vvhg1/clp-keycaps/step/CLP_Base_Tilt7_1_5u.step

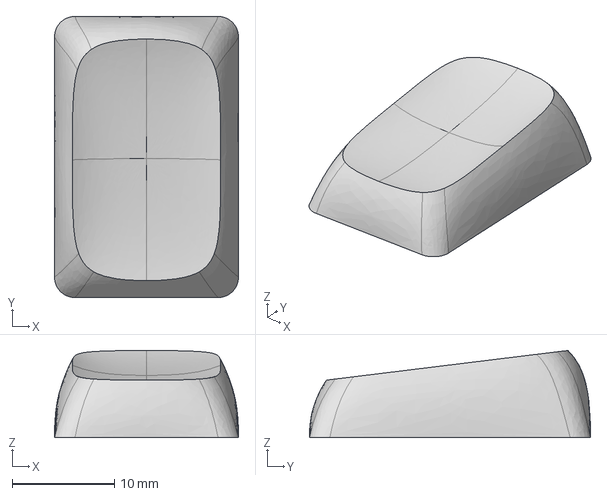
[picture p20: CAD file, 2026-10-05]
step/CLP_Base_Tilt7_1_5u.step
18.0 x 27.5 x 8.52 mm
