vvhg1/clp-keycaps/stl/CLP_Tilt7 v8.stl

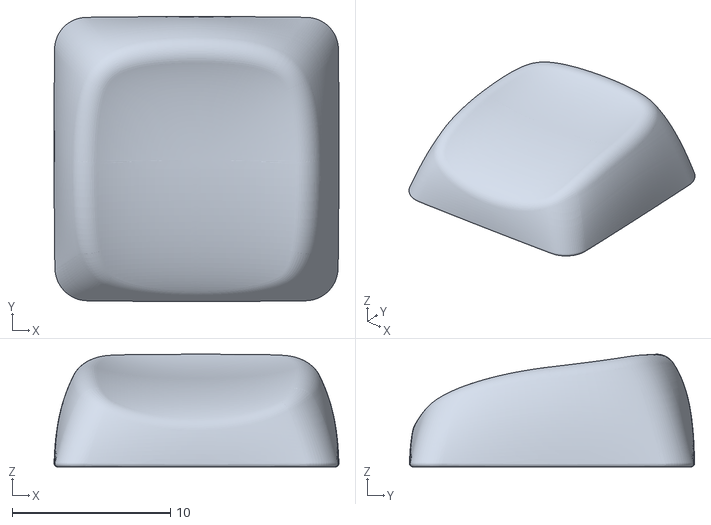
[picture p21: CAD file, 2023-11-12]
stl/CLP_Tilt7 v8.stl
18.0 x 18.0 x 7.11
