vvhg1/clp-keycaps/step/CLP_Base_Tilt14_R4.step

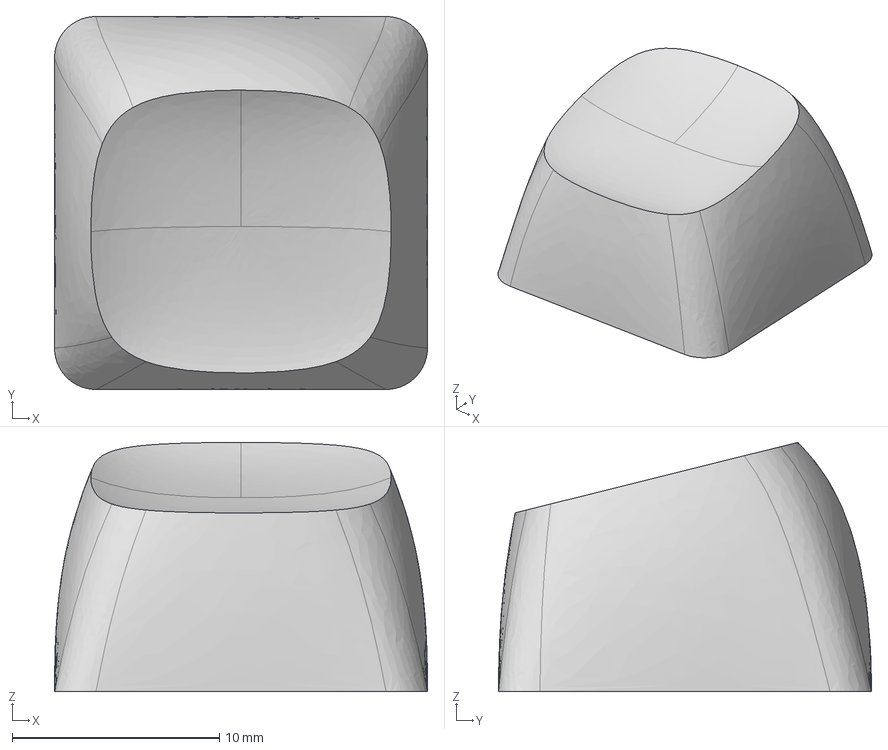
[picture p22: CAD file, 2026-10-05]
step/CLP_Base_Tilt14_R4.step
18.0 x 18.0 x 12.0 mm
