vvhg1/clp-keycaps/step/CLP_Base_Tilt14_Doubleslant.step

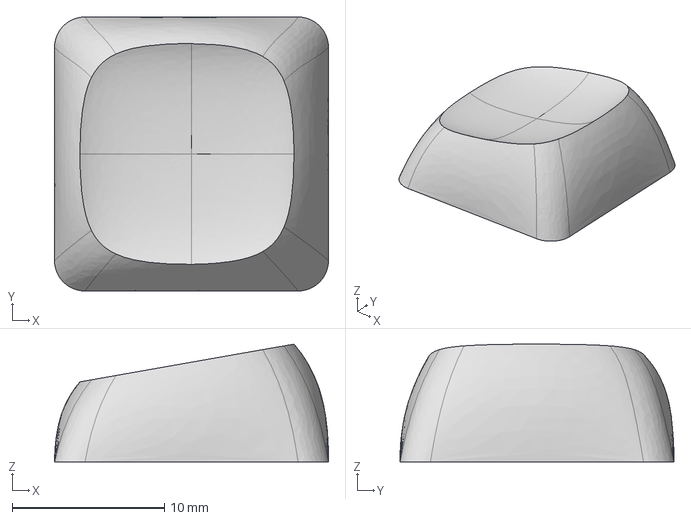
[picture p23: CAD file, 2026-10-05]
step/CLP_Base_Tilt14_Doubleslant.step
18.0 x 18.0 x 7.74 mm
