vvhg1/clp-keycaps/stl/CLP_Tilt7_1_5u v13.stl

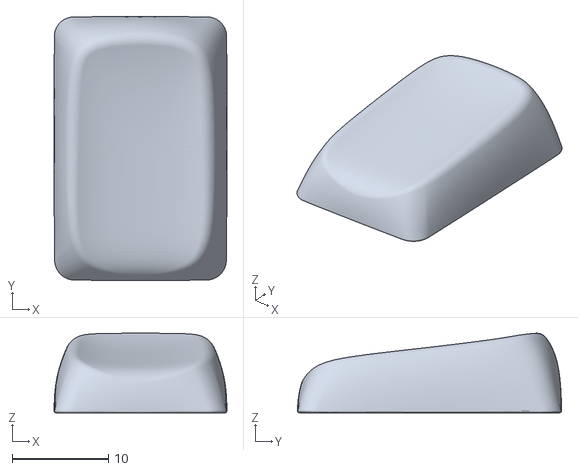
[picture p24: CAD file, 2023-11-12]
stl/CLP_Tilt7_1_5u v13.stl
18.0 x 27.5 x 8.30
