vvhg1/clp-keycaps/stl/CLP_Dished_Tilt14 v3.stl

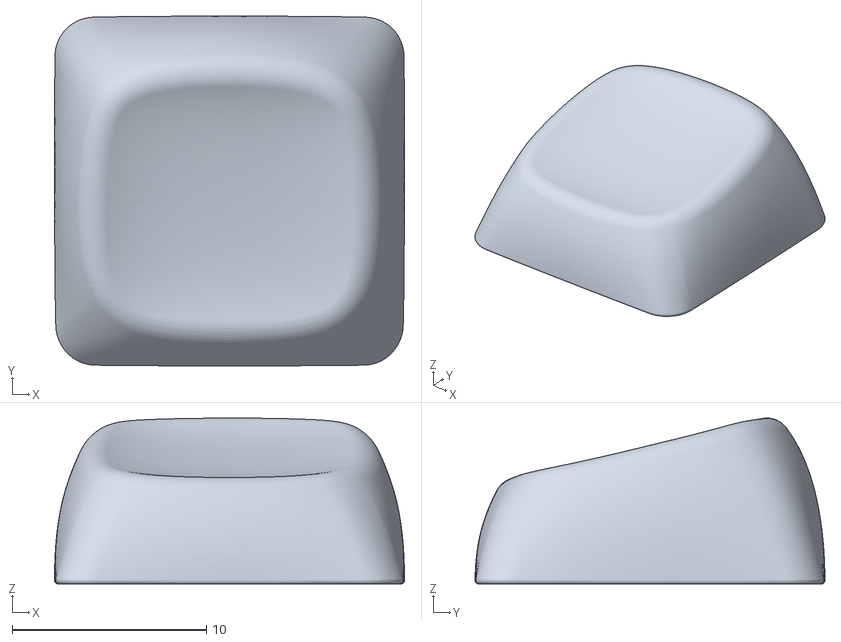
[picture p25: CAD file, 2023-11-12]
stl/CLP_Dished_Tilt14 v3.stl
18.0 x 18.0 x 8.53
