vvhg1/clp-keycaps/step/CLP_Base_Tilt7_R4.step

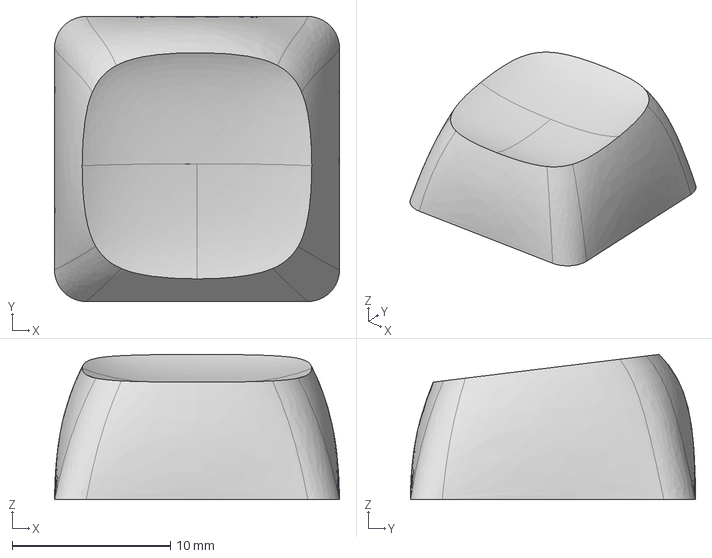
[picture p26: CAD file, 2026-10-05]
step/CLP_Base_Tilt7_R4.step
18.0 x 18.0 x 9.17 mm
