vvhg1/clp-keycaps/step/CLP_Base_Tilt14.step

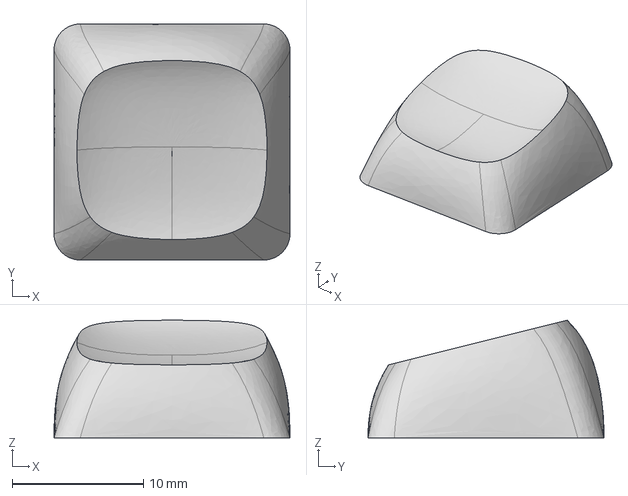
[picture p27: CAD file, 2026-10-05]
step/CLP_Base_Tilt14.step
18.0 x 18.0 x 8.97 mm
