vvhg1/clp-keycaps/step/CLP_Base.step

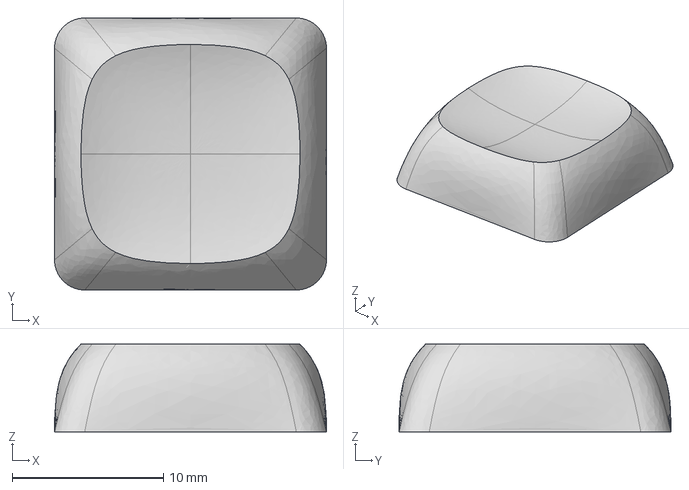
[picture p28: CAD file, 2026-10-05]
step/CLP_Base.step
18.0 x 18.0 x 5.80 mm
