vvhg1/clp-keycaps/step/CLP_Base_Tilt7_Slant10.step

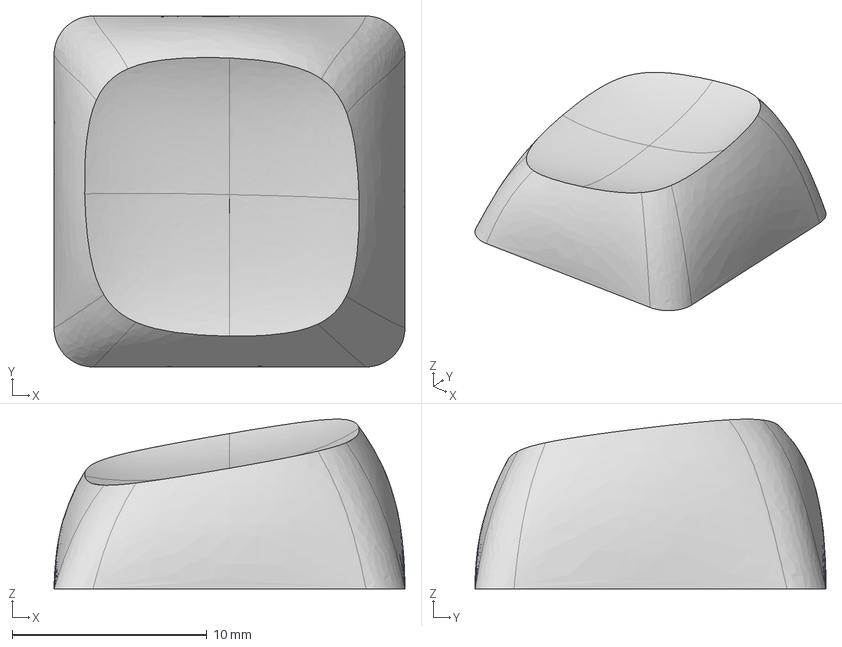
[picture p29: CAD file, 2026-10-05]
step/CLP_Base_Tilt7_Slant10.step
18.0 x 18.0 x 8.70 mm
