vvhg1/clp-keycaps/step/CLP_Tilt14_Slant10.step

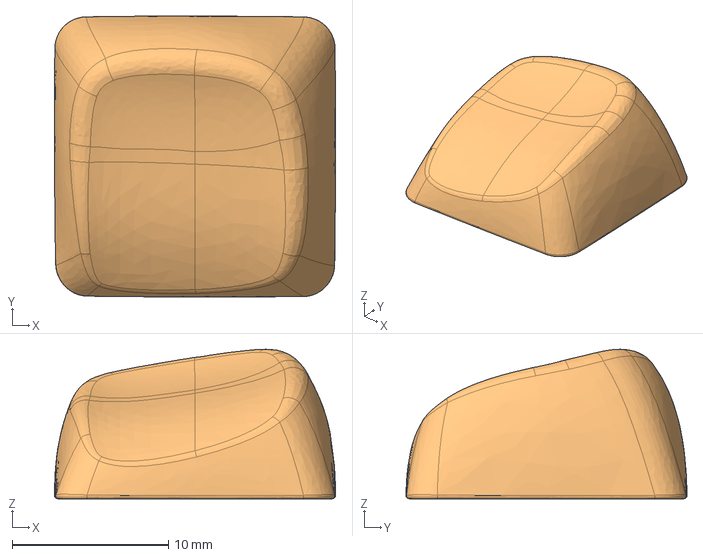
[picture p30: CAD file, 2026-10-05]
step/CLP_Tilt14_Slant10.step
18.0 x 18.0 x 9.58 mm
