vvhg1/clp-keycaps/step/CLP_Base_Tilt14_Slant10.step

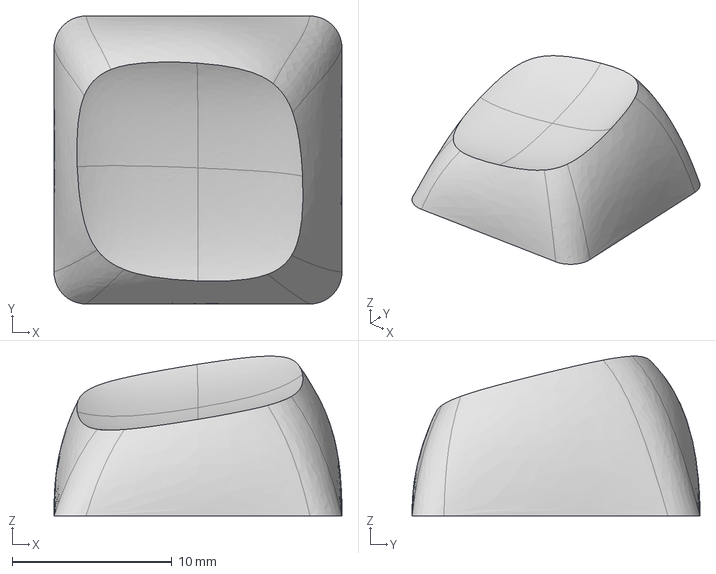
[picture p31: CAD file, 2026-10-05]
step/CLP_Base_Tilt14_Slant10.step
18.0 x 18.0 x 9.99 mm
