vvhg1/clp-keycaps/step/CLP_Tilt7_Slant10.step

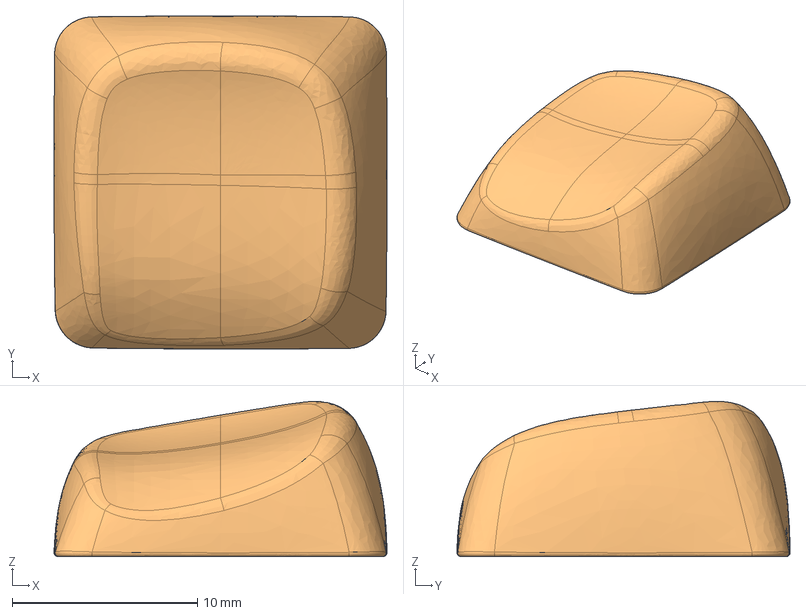
[picture p32: CAD file, 2026-10-05]
step/CLP_Tilt7_Slant10.step
18.0 x 18.0 x 8.38 mm
