vvhg1/clp-keycaps/step/MX Plug Mushroom v4.step

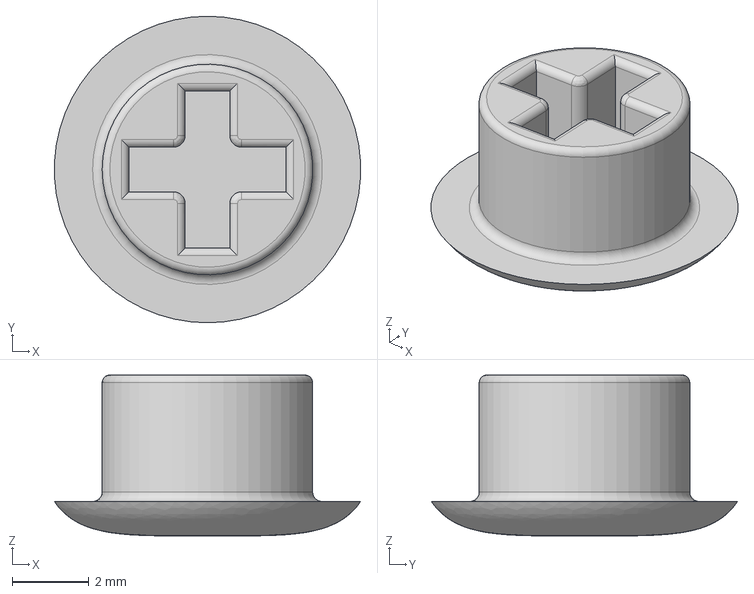
[picture p33: CAD file, 2026-10-05]
step/MX Plug Mushroom v4.step
7.99 x 8.00 x 4.20 mm
